manthelt/Bitstream-Evolution-FilterBoard/Bitstream_Evolution_Filterboard/Images/2738504.png

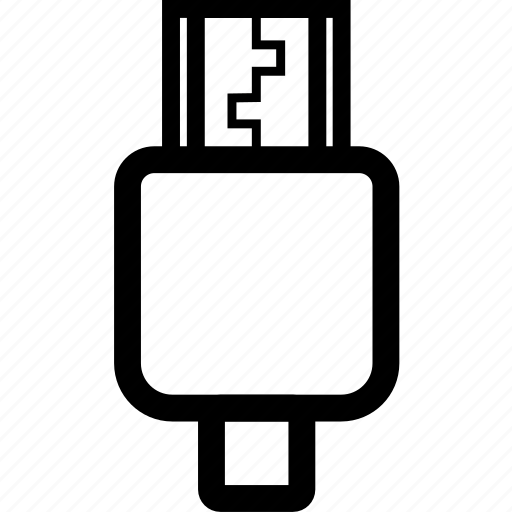
Bitstream_Evolution_Filterboard/Images/2738504.png
